masonandrewmann/birds_proj/freq_detect/AsyncAnalog.cpp

// Analog IO

#include "wiring_private.h"
#include "pins_arduino.h"

extern uint8_t analog_reference;

void analogReadSetup(uint8_t pin)
{
#if defined(analogPinToChannel)
  pin = analogPinToChannel(pin);
#elif defined(__AVR_ATmega1280__) || defined(__AVR_ATmega2560__)
  if (pin >= 54) pin -= 54; // allow for channel or pin numbers
#elif defined(__AVR_ATmega32U4__)
  if (pin >= 18) pin -= 18; // allow for channel or pin numbers
#elif defined(__AVR_ATmega1284__) || defined(__AVR_ATmega1284P__) || defined(__AVR_ATmega644__) || defined(__AVR_ATmega644A__) || defined(__AVR_ATmega644P__) || defined(__AVR_ATmega644PA__)
  if (pin >= 24) pin -= 24; // allow for channel or pin numbers
#else
  if (pin >= 14) pin -= 14; // allow for channel or pin numbers
#endif

#if defined(ADCSRB) && defined(MUX5)
  // the MUX5 bit of ADCSRB selects whether we're reading from channels
  // 0 to 7 (MUX5 low) or 8 to 15 (MUX5 high).
  ADCSRB = (ADCSRB & ~(1 << MUX5)) | (((pin >> 3) & 0x01) << MUX5);
#endif
  
  // set the analog reference (high two bits of ADMUX) and select the
  // channel (low 4 bits).  this also sets ADLAR (left-adjust result)
  // to 0 (the default).
#if defined(ADMUX)
#if defined(__AVR_ATtiny25__) || defined(__AVR_ATtiny45__) || defined(__AVR_ATtiny85__)
  ADMUX = (analog_reference << 4) | (pin & 0x07);
#else
  ADMUX = (analog_reference << 6) | (pin & 0x07);
#endif
#endif

  // without a delay, we seem to read from the wrong channel
  //delay(1);

  // Set ADIE in ADCSRA (0x7A) to enable the ADC interrupt.
  // Without this, the internal interrupt will not trigger.
  ADCSRA |= B00001000;    
}

void analogReadStart()
{
#if defined(ADCSRA) && defined(ADCL)
  // start the conversion
  sbi(ADCSRA, ADSC);
#endif

  // Set ADSC in ADCSRA (0x7A) to start the ADC conversion
  ADCSRA |=B01000000;
}

int analogReadStatus()
{
  // ADSC is cleared when the conversion finishes
  return bit_is_set(ADCSRA, ADSC);
}

int analogReadGetValue()
{
  uint8_t low, high;
  
  // we have to read ADCL first; doing so locks both ADCL
  // and ADCH until ADCH is read.  reading ADCL second would
  // cause the results of each conversion to be discarded,
  // as ADCL and ADCH would be locked when it completed.
  low  = ADCL;
  high = ADCH;

  // combine the two bytes
  return (high << 8) | low;
}
